semarc-gx8kvu/PicoRX/SEMARC/kicad-files-temp/Alister_G3ZBU/IMG_20260323_111321_top.jpeg

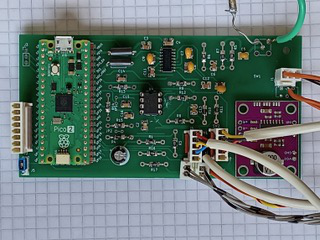
SEMARC/kicad-files-temp/Alister_G3ZBU/IMG_20260323_111321_top.jpeg
