semarc-gx8kvu/PicoRX/SEMARC/kicad-files-temp/Alister_G3ZBU/IMG_20260323_111336_bot.jpeg

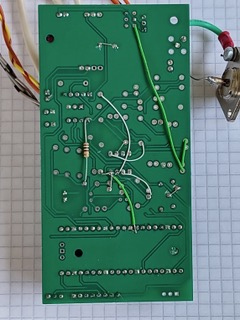
SEMARC/kicad-files-temp/Alister_G3ZBU/IMG_20260323_111336_bot.jpeg
