semarc-gx8kvu/PicoRX/SEMARC/kicad-files-temp/Alister_G3ZBU/IMG_20260323_111412_bot.jpg

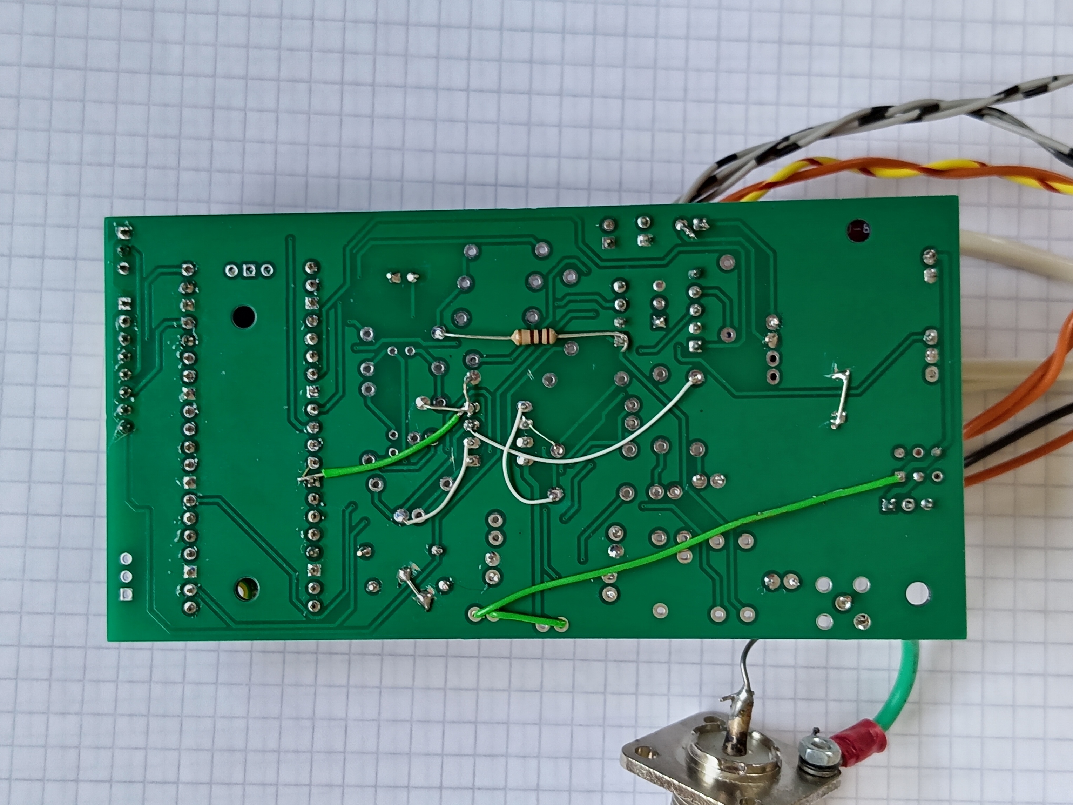
SEMARC/kicad-files-temp/Alister_G3ZBU/IMG_20260323_111412_bot.jpg
