semarc-gx8kvu/PicoRX/SEMARC/kicad-files-temp/Alister_G3ZBU/scanPicoRX_BOT.jpeg

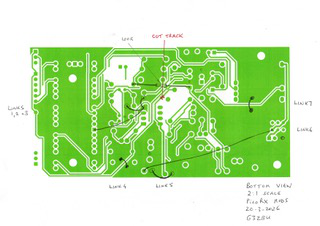
SEMARC/kicad-files-temp/Alister_G3ZBU/scanPicoRX_BOT.jpeg
