semarc-gx8kvu/PicoRX/SEMARC/kicad-files-temp/Alister_G3ZBU/scanPicoRX_TOP.jpg

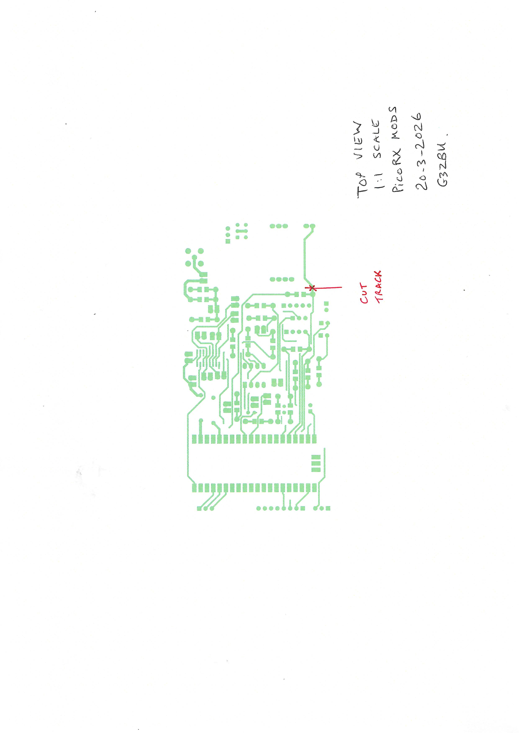
SEMARC/kicad-files-temp/Alister_G3ZBU/scanPicoRX_TOP.jpg
