semarc-gx8kvu/PicoRX/SEMARC/kicad-files-temp/Alister_G3ZBU/scanPicoRXiclegs.jpeg

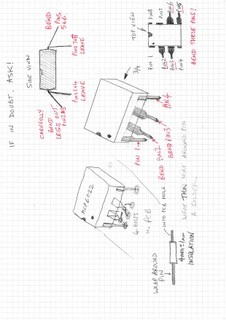
SEMARC/kicad-files-temp/Alister_G3ZBU/scanPicoRXiclegs.jpeg
